jarkman/gianttentacle/TentacleSensingWemos/Node.h

#ifndef NODE_H

#define NODE_H

#include <Wire.h>
#include <LSM303.h> // polulu library
#include <VL53L0X.h> // polulu library - uses less memory than the adafruit one


class Node
{
  public:
    int index;
    
    LSM303* compass;  // from Polulu example
    VL53L0X* leftRanger;
    VL53L0X* rightRanger;
    int leftMuxAddress;
    int rightMuxAddress;
    boolean hasRange;
    
    

  public:
    float heading; // absolute heading
    float normalisedHeading; // relative to base
    float relativeAngle;
    float targetAngle; // just for display purposes
    float length;
    float leftRange;
    float rightRange; 
    // current position of the node end, where x is out-from-the-wall and y is left-right
    float x; 
    float y;
    float targetX;
    float targetY;
    
    LSM303::vector<int16_t> running_min = {32767, 32767, 32767}, running_max = {-32768, -32768, -32768};


    Node( int _index, float _length, int _leftMux, int _rightMux, boolean _hasRange );

    void setup();
    void loop();
    void log();
    void calibrateCompass();

  private:
    void setupRangers();
    void setupRanger(VL53L0X* ranger);
    void setupCompass();
    float readRanger(VL53L0X* ranger);
    void loopCompass();
    void selectLeftMux();
    void selectRightMux();
    
};

#endif NODE_H
